azzeloof/snek/gateware/snekgen.v

/*
snekgen.v
snek
Adam Zeloof
11/27/2020
*/

module snekgen(
  input clk,
  input frame_clk,
  input rst,
  input [9:0] hpos,
  input [9:0] vpos,
  input grow_flag,
  input [2:0] dir,
  input run,
  output snek_loc,
  output [5:0] head_h,
  output [5:0] head_v,
  output [7:0] body_counter,
  output dead
);
  
  parameter maxlen = 16;//768; this is really short, but I was running tin problems making everything fit.

  genvar j; // index for generate-block for loops
  reg [11:0] i; // index for initial/always for loops
  reg [11:0] k;

  reg [5:0] body_h [maxlen-1:0];
  reg [5:0] body_v [maxlen-1:0];
  reg [7:0] body_counter = 1;
  
  // Put snek head in screen center, all other segments off-screen
  initial begin
    body_h[0] <= 15;
    body_v[0] <= 11;
    for (i=1; i<maxlen; i++) begin
      body_h[i] <= 42;
      body_v[i] <= 42;
    end
  end
 
  wire [5:0] head_h;
  wire [5:0] head_v;

  assign head_h = body_h[0];
  assign head_v = body_v[0];
  
  // Each bit corresponds to one segment of the snek body
  //wire [maxlen-1:0] snek_locs; // Bits HIGH when hpos and vpos intersect with the segment location
  reg [maxlen-1:0] snek_locs;
  reg snek_loc;
  
  reg dead;
  reg do_grow;
  reg did_grow;

  always @(posedge clk) begin
    if (grow_flag) begin
      do_grow <= 1;
    end
    if (did_grow) begin
      do_grow <= 0;
    end
    for (k=0; k<maxlen; k=k+1) begin
      snek_locs[k] <= (hpos > body_h[k]*20) & (hpos < (body_h[k]+1)*20) & (vpos > body_v[k]*20) & (vpos < (body_v[k]+1)*20);
    end
    snek_loc = |snek_locs;
  end

  always @(posedge frame_clk) begin
    if (run) begin // only move when the game is running (not during splashscreen)
      if (did_grow) begin
        did_grow <= 0;
      end
      if (do_grow) begin
        // Bring the next body segment onto the screen
        body_counter <= body_counter + 1;
        body_h[body_counter] <= body_h[body_counter-1];
        body_v[body_counter] <= body_v[body_counter-1];
        did_grow <= 1;
      end
      // Switch directions
      if (dir == 0) begin
        body_h[0] <= body_h[0] - 1;
      end else if (dir == 1) begin
        body_h[0] <= body_h[0] + 1;
      end else if (dir == 2) begin
        body_v[0] <= body_v[0] + 1;
      end else if (dir == 3) begin
        body_v[0] <= body_v[0] - 1;
      end
      // Move all on-screen segments
      for (i=1; i<maxlen; i++) begin
        // unused body segments are kept at 42, 42
        if ((body_h[i] != 42) & (body_v[i] != 42)) begin // if the segment is on-screen
          body_h[i] <= body_h[i-1];
          body_v[i] <= body_v[i-1];
        end
      end
    end
    // Reset to initial state
    if (rst) begin // lets reset to the original state
      body_h[0] <= 15;
      body_v[0] <= 11;
      for (i=1; i<maxlen; i++) begin
        body_h[i] <= 42;
        body_v[i] <= 42;
        body_counter <= 1;
      end
    end
  end

  // Check for snek death
  always @(negedge frame_clk) begin
    if ((head_h > 31) | (head_v > 23)) begin // Departed screen on the right
      dead <= 1;
    end
    for (i=1; i<maxlen; i++) begin  // Self intersection
      if ((head_h == body_h[i]) & (head_v == body_v[i])) begin
        dead <= 1;
      end
    end
    if (rst) begin
      dead <= 0;
    end
  end
  
endmodule
